compukidmike/Defcon29/Firmware/Source/DC29/src/ASF/common/services/usb/class/hid/device/kbd/udi_hid_kbd.c

/**
 * \file
 *
 * \brief USB Device Human Interface Device (HID) keyboard interface.
 *
 * Copyright (c) 2009-2018 Microchip Technology Inc. and its subsidiaries.
 *
 * \asf_license_start
 *
 * \page License
 *
 * Subject to your compliance with these terms, you may use Microchip
 * software and any derivatives exclusively with Microchip products.
 * It is your responsibility to comply with third party license terms applicable
 * to your use of third party software (including open source software) that
 * may accompany Microchip software.
 *
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
 * \asf_license_stop
 *
 */
/*
 * Support and FAQ: visit <a href="https://www.microchip.com/support/">Microchip Support</a>
 */

#include "conf_usb.h"
#include "usb_protocol.h"
#include "udd.h"
#include "udc.h"
#include "udi_hid.h"
#include "udi_hid_kbd.h"
#include <string.h>

/**
 * \ingroup udi_hid_keyboard_group
 * \defgroup udi_hid_keyboard_group_udc Interface with USB Device Core (UDC)
 *
 * Structures and functions required by UDC.
 *
 * @{
 */

bool udi_hid_kbd_enable(void);
void udi_hid_kbd_disable(void);
bool udi_hid_kbd_setup(void);
uint8_t udi_hid_kbd_getsetting(void);

//! Global structure which contains standard UDI interface for UDC
UDC_DESC_STORAGE udi_api_t udi_api_hid_kbd = {
	.enable = (bool(*)(void))udi_hid_kbd_enable,
	.disable = (void (*)(void))udi_hid_kbd_disable,
	.setup = (bool(*)(void))udi_hid_kbd_setup,
	.getsetting = (uint8_t(*)(void))udi_hid_kbd_getsetting,
	.sof_notify = NULL,
};
//@}


/**
 * \ingroup udi_hid_keyboard_group
 * \defgroup udi_hid_keyboard_group_internal Implementation of UDI HID keyboard
 *
 * Class internal implementation
 * @{
 */

/**
 * \name Internal defines and variables to manage HID keyboard
 */
//@{

//! Size of report for standard HID keyboard
#define UDI_HID_KBD_REPORT_SIZE  9 //added report ID 8


//! To store current rate of HID keyboard
COMPILER_WORD_ALIGNED
		static uint8_t udi_hid_kbd_rate;
//! To store current protocol of HID keyboard
COMPILER_WORD_ALIGNED
		static uint8_t udi_hid_kbd_protocol;
//! To store report feedback from USB host
COMPILER_WORD_ALIGNED
		static uint8_t udi_hid_kbd_report_set;
//! To signal if a valid report is ready to send
static bool udi_hid_kbd_b_report_valid;
//! Report ready to send
static uint8_t udi_hid_kbd_report[UDI_HID_KBD_REPORT_SIZE];
//! Signal if a report transfer is on going
//static bool udi_hid_kbd_b_report_trans_ongoing;
//! Buffer used to send report
COMPILER_WORD_ALIGNED
		static uint8_t
		udi_hid_kbd_report_trans[UDI_HID_KBD_REPORT_SIZE];

//@}

//! HID report descriptor for standard HID keyboard
UDC_DESC_STORAGE udi_hid_kbd_report_desc_t udi_hid_kbd_report_desc = {
	{
				0x05, 0x01,	/* Usage Page (Generic Desktop)      */
				0x09, 0x06,	/* Usage (Keyboard)                  */
				0xA1, 0x01,	/* Collection (Application)          */
				0x85, 0x01,        //   Report ID (1)
				0x05, 0x07,	/* Usage Page (Keyboard)             */
				0x19, 224,	/* Usage Minimum (224)               */
				0x29, 231,	/* Usage Maximum (231)               */
				0x15, 0x00,	/* Logical Minimum (0)               */
				0x25, 0x01,	/* Logical Maximum (1)               */
				0x75, 0x01,	/* Report Size (1)                   */
				0x95, 0x08,	/* Report Count (8)                  */
				0x81, 0x02,	/* Input (Data, Variable, Absolute)  */
				0x81, 0x01,	/* Input (Constant)                  */
				0x19, 0x00,	/* Usage Minimum (0)                 */
				0x29, 115,	/* Usage Maximum (101)               */
				0x15, 0x00,	/* Logical Minimum (0)               */
				0x25, 115,	/* Logical Maximum (101)             */
				0x75, 0x08,	/* Report Size (8)                   */
				0x95, 0x06,	/* Report Count (6)                  */
				0x81, 0x00,	/* Input (Data, Array)               */
				0x05, 0x08,	/* Usage Page (LED)                  */
				0x19, 0x01,	/* Usage Minimum (1)                 */
				0x29, 0x05,	/* Usage Maximum (5)                 */
				0x15, 0x00,	/* Logical Minimum (0)               */
				0x25, 0x01,	/* Logical Maximum (1)               */
				0x75, 0x01,	/* Report Size (1)                   */
				0x95, 0x05,	/* Report Count (5)                  */
				0x91, 0x02,	/* Output (Data, Variable, Absolute) */
				0x95, 0x03,	/* Report Count (3)                  */
				0x91, 0x01,	/* Output (Constant)                 */
				0xC0,	/* End Collection                    */
				0x05, 0x0C,        // Usage Page (Consumer)
				0x09, 0x01,        // Usage (Consumer Control)
				0xA1, 0x01,        // Collection (Application)
				0x85, 0x02,        //   Report ID (2)
				0x05, 0x0C,        //   Usage Page (Consumer)
				0x15, 0x00,        //   Logical Minimum (0)
				0x25, 0x01,        //   Logical Maximum (1)
				0x75, 0x01,        //   Report Size (1)
				0x95, 0x08,        //   Report Count (8)
				0x09, 0xB5,        //   Usage (Scan Next Track)
				0x09, 0xB6,        //   Usage (Scan Previous Track)
				0x09, 0xB7,        //   Usage (Stop)
				0x09, 0xB8,        //   Usage (Eject)
				0x09, 0xCD,        //   Usage (Play/Pause)
				0x09, 0xE2,        //   Usage (Mute)
				0x09, 0xE9,        //   Usage (Volume Increment)
				0x09, 0xEA,        //   Usage (Volume Decrement)
				0x81, 0x02,        //   Input (Data,Var,Abs,No Wrap,Linear,Preferred State,No Null Position)
				0xC0,              // End Collection
			}
};

/**
 * \name Internal routines
 */
//@{

/**
 * \brief Changes keyboard report states (like LEDs)
 *
 * \param rate       New rate value
 *
 */
static bool udi_hid_kbd_setreport(void);

/**
 * \brief Send the report
 *
 * \return \c 1 if send on going, \c 0 if delay.
 */
static bool udi_hid_kbd_send_report(void);

/**
 * \brief Callback called when the report is sent
 *
 * \param status     UDD_EP_TRANSFER_OK, if transfer is completed
 * \param status     UDD_EP_TRANSFER_ABORT, if transfer is aborted
 * \param nb_sent    number of data transfered
 *
 * \return \c 1 if function was successfully done, otherwise \c 0.
 */
static void udi_hid_kbd_report_sent(udd_ep_status_t status, iram_size_t nb_sent,
		udd_ep_id_t ep);

/**
 * \brief Callback called to update report from USB host
 * udi_hid_kbd_report_set is updated before callback execution
 */
static void udi_hid_kbd_setreport_valid(void);

//@}


//--------------------------------------------
//------ Interface for UDI HID level

bool udi_hid_kbd_enable(void)
{
	// Initialize internal values
	udi_hid_kbd_rate = 0;
	udi_hid_kbd_protocol = 0;
	udi_hid_kbd_b_report_trans_ongoing = false;
	memset(udi_hid_kbd_report, 0, UDI_HID_KBD_REPORT_SIZE);
	udi_hid_kbd_report[0] = 1;
	udi_hid_kbd_b_report_valid = false;
	return UDI_HID_KBD_ENABLE_EXT();
}


void udi_hid_kbd_disable(void)
{
	UDI_HID_KBD_DISABLE_EXT();
}


bool udi_hid_kbd_setup(void)
{
	return udi_hid_setup(&udi_hid_kbd_rate,
								&udi_hid_kbd_protocol,
								(uint8_t *) &udi_hid_kbd_report_desc,
								udi_hid_kbd_setreport);
}


uint8_t udi_hid_kbd_getsetting(void)
{
	return 0;
}


static bool udi_hid_kbd_setreport(void)
{
	if ((USB_HID_REPORT_TYPE_OUTPUT == (udd_g_ctrlreq.req.wValue >> 8))
			&& (0 == (0xFF & udd_g_ctrlreq.req.wValue))
			&& (1 == udd_g_ctrlreq.req.wLength)) {
		// Report OUT type on report ID 0 from USB Host
		udd_g_ctrlreq.payload = &udi_hid_kbd_report_set;
		udd_g_ctrlreq.callback = udi_hid_kbd_setreport_valid;
		udd_g_ctrlreq.payload_size = 1;
		return true;
	}
	return false;
}


//--------------------------------------------
//------ Interface for application

bool udi_hid_kbd_modifier_up(uint8_t modifier_id)
{
	irqflags_t flags = cpu_irq_save();

	// Fill report
	udi_hid_kbd_report[1] &= ~(unsigned)modifier_id;
	udi_hid_kbd_b_report_valid = true;

	// Send report
	udi_hid_kbd_send_report();

	cpu_irq_restore(flags);
	return true;
}


bool udi_hid_kbd_modifier_down(uint8_t modifier_id)
{
	irqflags_t flags = cpu_irq_save();

	// Fill report
	udi_hid_kbd_report[1] |= modifier_id;
	udi_hid_kbd_b_report_valid = true;

	// Send report
	udi_hid_kbd_send_report();

	cpu_irq_restore(flags);
	return true;
}


bool udi_hid_kbd_up(uint8_t key_id)
{
	uint8_t i;

	irqflags_t flags = cpu_irq_save();

	// Fill report
	for (i = 3; i < UDI_HID_KBD_REPORT_SIZE; i++) {
		if (0 == udi_hid_kbd_report[i]) {
			// Already removed
			cpu_irq_restore(flags);
			return true;
		}
		if (key_id == udi_hid_kbd_report[i])
			break;
	}
	if (UDI_HID_KBD_REPORT_SIZE == i) {
		// Already removed
		cpu_irq_restore(flags);
		return true;
	}
	// Remove key and shift
	while (i < (UDI_HID_KBD_REPORT_SIZE - 1)) {
		udi_hid_kbd_report[i] = udi_hid_kbd_report[i + 1];
		i++;
	}
	udi_hid_kbd_report[UDI_HID_KBD_REPORT_SIZE - 1] = 0x00;
	udi_hid_kbd_b_report_valid = true;

	// Send report
	udi_hid_kbd_send_report();

	cpu_irq_restore(flags);
	return true;
}


bool udi_hid_kbd_down(uint8_t key_id)
{
	uint8_t i;

	irqflags_t flags = cpu_irq_save();

	// Fill report
	for (i = 3; i < UDI_HID_KBD_REPORT_SIZE; i++) {
		if (0 == udi_hid_kbd_report[i])
			break;
		if (key_id == udi_hid_kbd_report[i]) {
			// Already in array
			cpu_irq_restore(flags);
			return true;
		}
	}

	if (UDI_HID_KBD_REPORT_SIZE == i) {
		// Array full

		cpu_irq_restore(flags);
		return false;
	}
	// Add key at the end of array
	udi_hid_kbd_report[i] = key_id;
	udi_hid_kbd_b_report_valid = true;

	// Send report
	udi_hid_kbd_send_report();

	// Enable IT
	cpu_irq_restore(flags);
	return true;
}

void udi_hid_media_down(uint8_t key_id){
	irqflags_t flags = cpu_irq_save();
	udi_hid_kbd_report[0] = 2;
	udi_hid_kbd_report[1] = key_id;
	memcpy(udi_hid_kbd_report_trans, udi_hid_kbd_report,2);
	udi_hid_kbd_b_report_valid = false;
	udi_hid_kbd_b_report_trans_ongoing = udd_ep_run(UDI_HID_KBD_EP_IN,false,udi_hid_kbd_report_trans,2,udi_hid_kbd_report_sent);
	udi_hid_kbd_report[0] = 1;
	udi_hid_kbd_report[3] = 0;
	cpu_irq_restore(flags);
}

void udi_hid_media_up(void){
	irqflags_t flags = cpu_irq_save();
	udi_hid_kbd_report[0] = 2;
	udi_hid_kbd_report[1] = 0;
	memcpy(udi_hid_kbd_report_trans, udi_hid_kbd_report,2);
	udi_hid_kbd_b_report_valid = false;
	udi_hid_kbd_b_report_trans_ongoing = udd_ep_run(UDI_HID_KBD_EP_IN,false,udi_hid_kbd_report_trans,2,udi_hid_kbd_report_sent);
	udi_hid_kbd_report[0] = 1;
	udi_hid_kbd_report[3] = 0;
	cpu_irq_restore(flags);
}


//--------------------------------------------
//------ Internal routines

static bool udi_hid_kbd_send_report(void)
{
	if (udi_hid_kbd_b_report_trans_ongoing)
		return false;
	memcpy(udi_hid_kbd_report_trans, udi_hid_kbd_report,
			UDI_HID_KBD_REPORT_SIZE);
	udi_hid_kbd_b_report_valid = false;
	udi_hid_kbd_b_report_trans_ongoing =
			udd_ep_run(	UDI_HID_KBD_EP_IN,
							false,
							udi_hid_kbd_report_trans,
							UDI_HID_KBD_REPORT_SIZE,
							udi_hid_kbd_report_sent);
	return udi_hid_kbd_b_report_trans_ongoing;
}

static void udi_hid_kbd_report_sent(udd_ep_status_t status, iram_size_t nb_sent,
		udd_ep_id_t ep)
{
	UNUSED(status);
	UNUSED(nb_sent);
	UNUSED(ep);
	udi_hid_kbd_b_report_trans_ongoing = false;
	if (udi_hid_kbd_b_report_valid) {
		udi_hid_kbd_send_report();
	}
}

static void udi_hid_kbd_setreport_valid(void)
{
	UDI_HID_KBD_CHANGE_LED(udi_hid_kbd_report_set);
}

//@}
